benkoren/papa-project-board/KiCad/papa-project-board.kicad_sch

## KiCad design KiCad/papa-project-board.kicad_sch (2026-02-10)

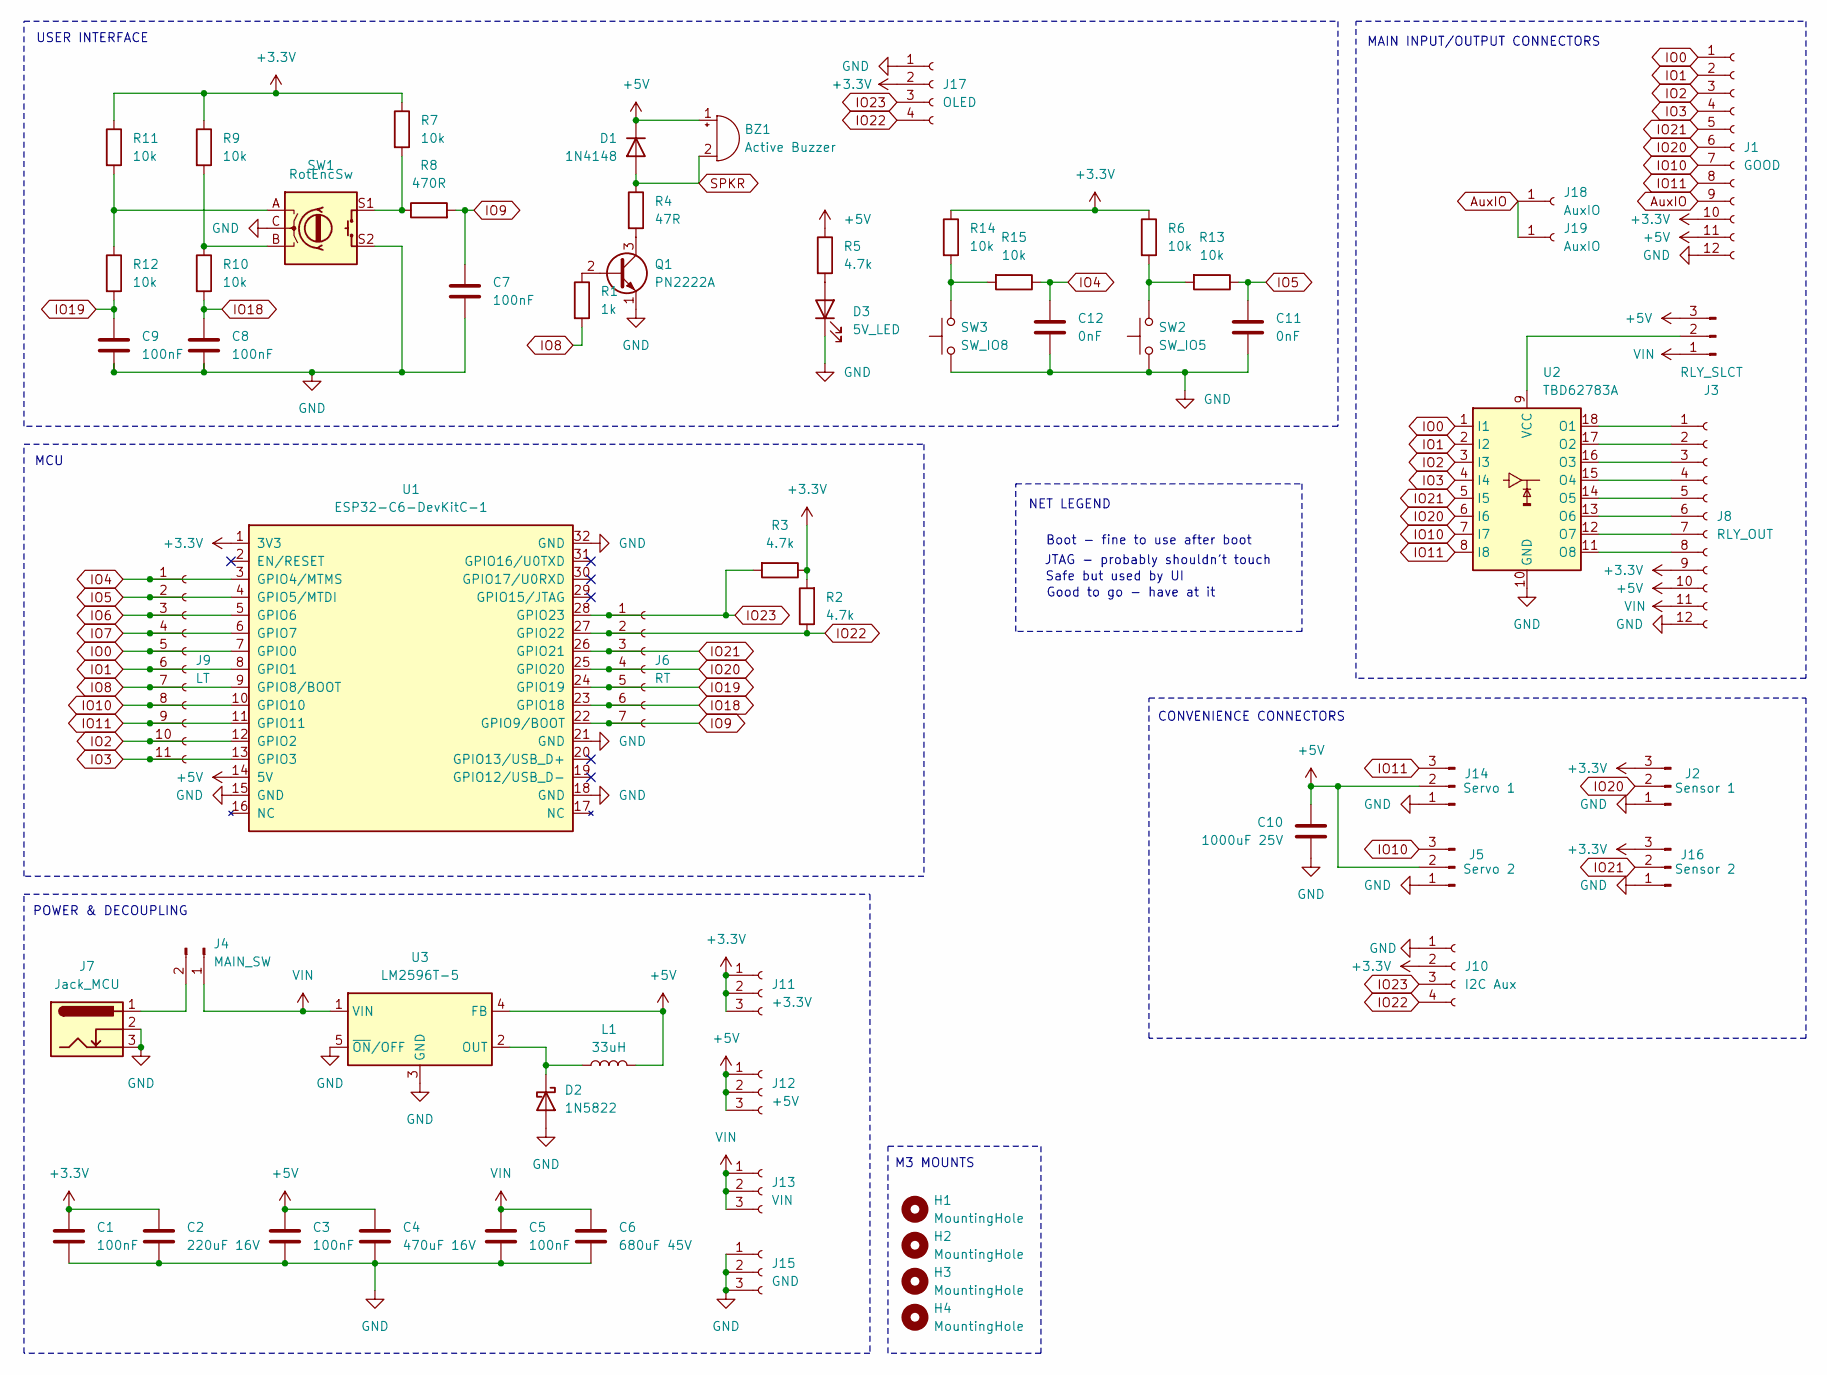
[picture p17: schematic papa-project-board.kicad_sch]

Parts:
BZ1: Active Buzzer; Buzzer_12x9.5RM7.6
C1, C3, C5, C7, C8, C9: 100nF; C_Disc_D5.0mm_W2.5mm_P5.00mm
C2: 220uF 16V; CP_Radial_D8.0mm_P2.50mm
C4: 470uF 16V; CP_Radial_D8.0mm_P2.50mm
C6: 680uF 45V; CP_Radial_D8.0mm_P2.50mm
C10: 1000uF 25V; CP_Radial_D12.5mm_P5.00mm
C11, C12: 0nF; C_Disc_D5.0mm_W2.5mm_P5.00mm
D1: 1N4148; D_DO-35_SOD27_P7.62mm_Horizontal
D2: 1N5822; D_DO-201AD_P15.24mm_Horizontal
D3: 5V_LED; LED_D5.0mm
H1, H2, H3, H4: MountingHole; MountingHole_3.2mm_M3
J1: GOOD; JST_XH_B12B-XH-A_1x12_P2.50mm_Vertical
J2: Sensor 1; JST_XH_B3B-XH-A_1x03_P2.50mm_Vertical
J3: RLY_SLCT; PinHeader_1x03_P2.54mm_Vertical
J4: MAIN_SW; PinHeader_1x02_P2.54mm_Vertical
J5: Servo 2; JST_XH_B3B-XH-A_1x03_P2.50mm_Vertical
J6: RT; PinSocket_1x07_P2.54mm_Vertical
J7: Jack_MCU; BarrelJack_Horizontal
J8: RLY_OUT; JST_XH_B12B-XH-A_1x12_P2.50mm_Vertical
J9: LT; PinSocket_1x11_P2.54mm_Vertical
J10: I2C Aux; JST_XH_B4B-XH-A_1x04_P2.50mm_Vertical
J11: +3.3V; PinSocket_1x03_P2.54mm_Vertical
J12: +5V; PinSocket_1x03_P2.54mm_Vertical
J13: VIN; PinSocket_1x03_P2.54mm_Vertical
J14: Servo 1; JST_XH_B3B-XH-A_1x03_P2.50mm_Vertical
J15: GND; PinSocket_1x03_P2.54mm_Vertical
J16: Sensor 2; JST_XH_B3B-XH-A_1x03_P2.50mm_Vertical
J17: OLED; PinSocket_1x04_P2.54mm_Vertical
J18, J19: AuxIO; TestPoint_Pad_D1.0mm
L1: 33uH; L_Toroid_Vertical_L14.7mm_W8.6mm_P5.58mm_Pulse_KM-1
Q1: PN2222A; TO-92_Inline
R1: 1k; R_Axial_DIN0207_L6.3mm_D2.5mm_P10.16mm_Horizontal
R2, R3, R5: 4.7k; R_Axial_DIN0207_L6.3mm_D2.5mm_P10.16mm_Horizontal
R4: 47R; R_Axial_DIN0207_L6.3mm_D2.5mm_P10.16mm_Horizontal
R6, R7, R9, R10, R11, R12, R13, R14, R15: 10k; R_Axial_DIN0207_L6.3mm_D2.5mm_P10.16mm_Horizontal
R8: 470R; R_Axial_DIN0207_L6.3mm_D2.5mm_P10.16mm_Horizontal
SW1: RotEncSw; RotaryEncoder_Alps_EC11E-Switch_Vertical_H20mm
SW2: SW_IO5; SW_PUSH-12mm_Wuerth-430476085716
SW3: SW_IO8; SW_PUSH-12mm_Wuerth-430476085716
U1: ESP32-C6-DevKitC-1
U2: TBD62783A; DIP-18_W7.62mm_Socket
U3: LM2596T-5; TO-220-5_Vertical

Connections:
+3.3V: C1.1, C2.1, J1.10, J2.3, J8.9, J10.2, J11.1, J11.2, J11.3, J16.3, J17.2, R2.2, R3.1, R6.1, R7.1, R9.1, R11.1, R14.1, U1.1 (3V3)
+5V: BZ1.1 (+), C3.1, C4.1, C10.1, D1.1 (K), J1.11, J3.3, J5.2, J8.10, J12.1, J12.2, J12.3, J14.2, L1.2, R5.1, U1.14 (5V), U3.4 (FB)
AuxIO: J1.9, J18.1, J19.1
GND: C1.2, C2.2, C3.2, C4.2, C5.2, C6.2, C7.2, C8.2, C9.2, C10.2, C11.2, C12.2, D2.2 (A), D3.1 (K), J1.12, J2.1, J5.1, J7.2, J7.3, J8.12, J10.1, J14.1, J15.1, J15.2, J15.3, J16.1, J17.1, Q1.1 (E), SW1.C, SW1.S2, SW2.1, SW3.1, U1.15 (GND), U1.18 (GND), U1.21 (GND), U1.32 (GND), U2.10 (GND), U3.3 (GND), U3.5 (~ON/OFF)
IO0: J1.1, J9.5, U1.7 (GPIO0), U2.1 (I1)
IO1: J1.2, J9.6, U1.8 (GPIO1), U2.2 (I2)
IO2: J1.3, J9.10, U1.12 (GPIO2), U2.3 (I3)
IO3: J1.4, J9.11, U1.13 (GPIO3), U2.4 (I4)
IO4: C12.1, J9.1, R15.1, U1.3 (GPIO4/MTMS)
IO5: C11.1, J9.2, R13.1, U1.4 (GPIO5/MTDI)
IO6: J9.3, U1.5 (GPIO6)
IO7: J9.4, U1.6 (GPIO7)
IO8: J9.7, R1.2, U1.9 (GPIO8/BOOT)
IO9: C7.1, J6.7, R8.2, U1.22 (GPIO9/BOOT)
IO10: J1.7, J5.3, J9.8, U1.10 (GPIO10), U2.7 (I7)
IO11: J1.8, J9.9, J14.3, U1.11 (GPIO11), U2.8 (I8)
IO18: C8.1, J6.6, R10.2, U1.23 (GPIO18)
IO19: C9.1, J6.5, R12.2, U1.24 (GPIO19)
IO20: J1.6, J2.2, J6.4, U1.25 (GPIO20), U2.6 (I6)
IO21: J1.5, J6.3, J16.2, U1.26 (GPIO21), U2.5 (I5)
IO22: J6.2, J10.4, J17.4, R2.1, U1.27 (GPIO22)
IO23: J6.1, J10.3, J17.3, R3.2, U1.28 (GPIO23)
unnamed: D2.1 (K), L1.1, U3.2 (OUT)
unnamed: D3.2 (A), R5.2
unnamed: J3.2, U2.9 (VCC)
unnamed: J4.2, J7.1
unnamed: J8.1, U2.18 (O1)
unnamed: J8.2, U2.17 (O2)
unnamed: J8.3, U2.16 (O3)
unnamed: J8.4, U2.15 (O4)
unnamed: J8.5, U2.14 (O5)
unnamed: J8.6, U2.13 (O6)
unnamed: J8.7, U2.12 (O7)
unnamed: J8.8, U2.11 (O8)
unnamed: Q1.2 (B), R1.1
unnamed: Q1.3 (C), R4.2
unnamed: R7.2, R8.1, SW1.S1
unnamed: R9.2, R10.1, SW1.B
unnamed: R11.2, R12.1, SW1.A
unnamed: R6.2, R13.2, SW2.2
unnamed: R14.2, R15.2, SW3.2
SPKR: BZ1.2 (-), D1.2 (A), R4.1
VIN: C5.1, C6.1, J3.1, J4.1, J8.11, J13.1, J13.2, J13.3, U3.1 (VIN)

Notes on the sheet:
JTAG - probably shouldn't touch
USER INTERFACE
Boot - fine to use after boot
Good to go - have at it
MAIN INPUT/OUTPUT CONNECTORS
MCU
M3 MOUNTS
Safe but used by UI
NET LEGEND
POWER & DECOUPLING
CONVENIENCE CONNECTORS
